J3T21/gAItar/solidworks/fret12_guide.SLDPRT

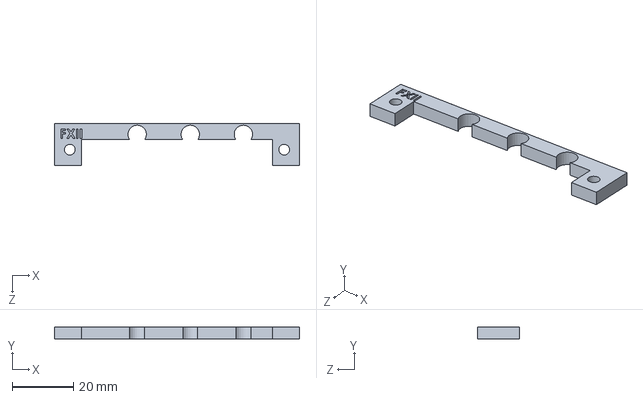
[picture p25: CAD file, 2025-05-29]
solidworks/fret12_guide.SLDPRT
80.0 x 4.00 x 13.8 mm
