J3T21/gAItar/solidworks/inside_helmet.SLDPRT

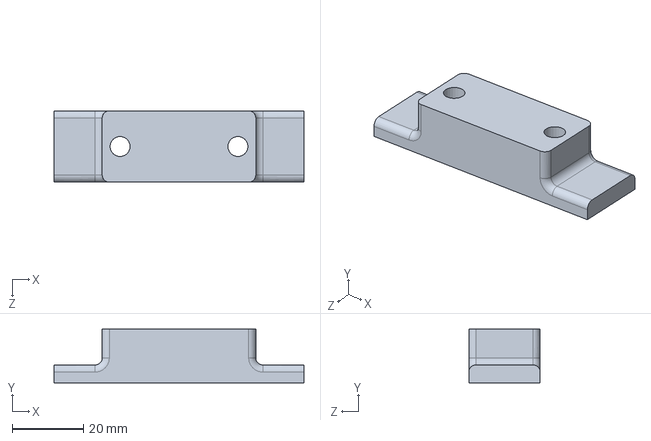
[picture p26: CAD file, 2025-05-04]
solidworks/inside_helmet.SLDPRT
70.0 x 15.0 x 20.0 mm
