J3T21/gAItar/solidworks/helmot_outer.SLDPRT

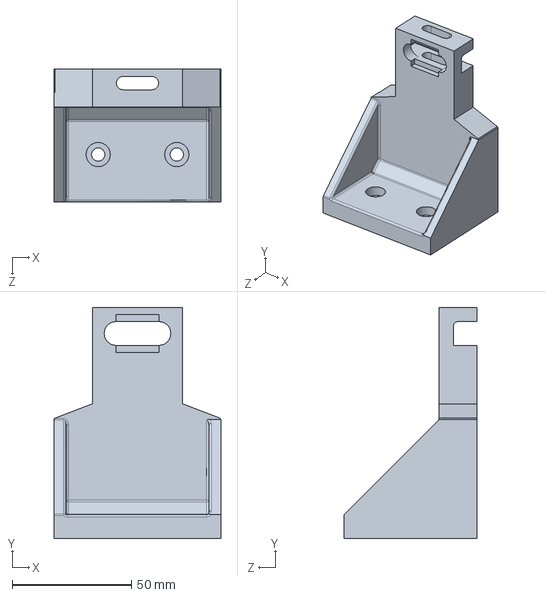
[picture p27: CAD file, 2025-05-04]
solidworks/helmot_outer.SLDPRT
70.0 x 97.0 x 56.0 mm
