J3T21/gAItar/solidworks/rh_26_3.SLDPRT

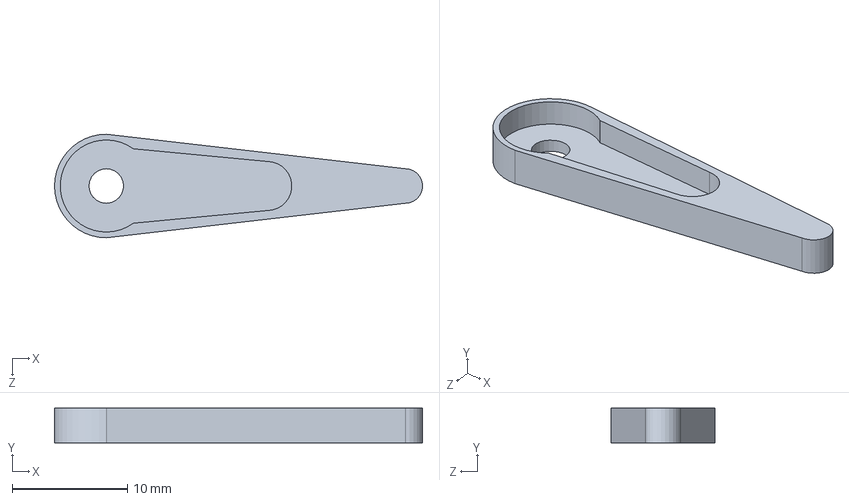
[picture p28: CAD file, 2025-04-07]
solidworks/rh_26_3.SLDPRT
32.0 x 3.00 x 9.00 mm
