J3T21/gAItar/solidworks/PCB_plate_n.STL

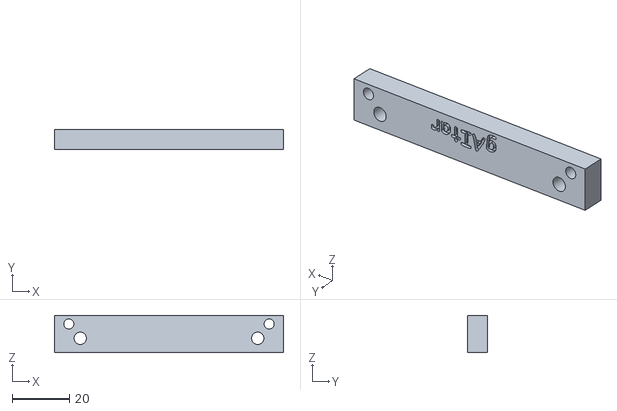
[picture p29: CAD file, 2025-04-07]
solidworks/PCB_plate_n.STL
80.0 x 7.00 x 13.0
