J3T21/gAItar/solidworks/rh_slotted.SLDPRT

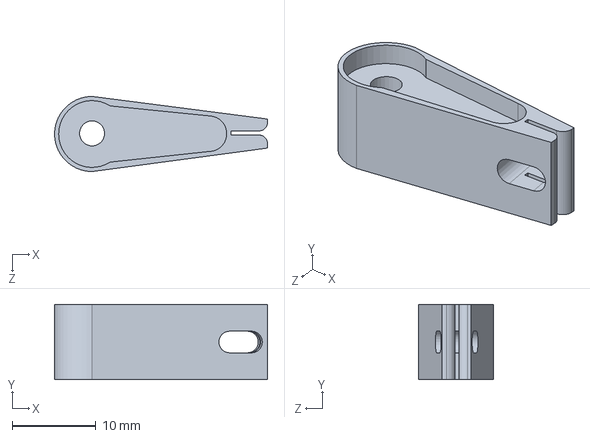
[picture p30: CAD file, 2025-04-07]
solidworks/rh_slotted.SLDPRT
25.5 x 9.00 x 9.00 mm
