J3T21/gAItar/solidworks/spacer.STL

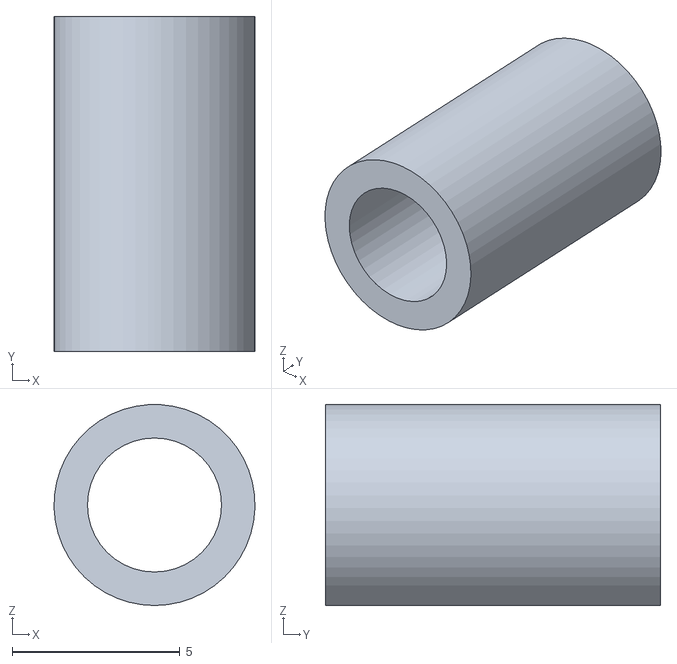
[picture p32: CAD file, 2025-04-07]
solidworks/spacer.STL
6.00 x 10.0 x 6.00
