J3T21/gAItar/solidworks/rh_27_3.STL

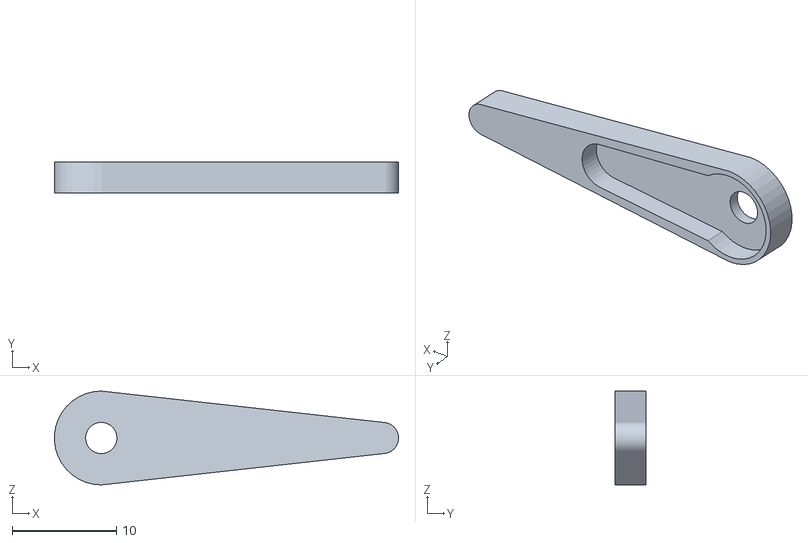
[picture p33: CAD file, 2025-04-07]
solidworks/rh_27_3.STL
33.0 x 3.00 x 9.00
