J3T21/gAItar/solidworks/rh_30_3_flex5.STL

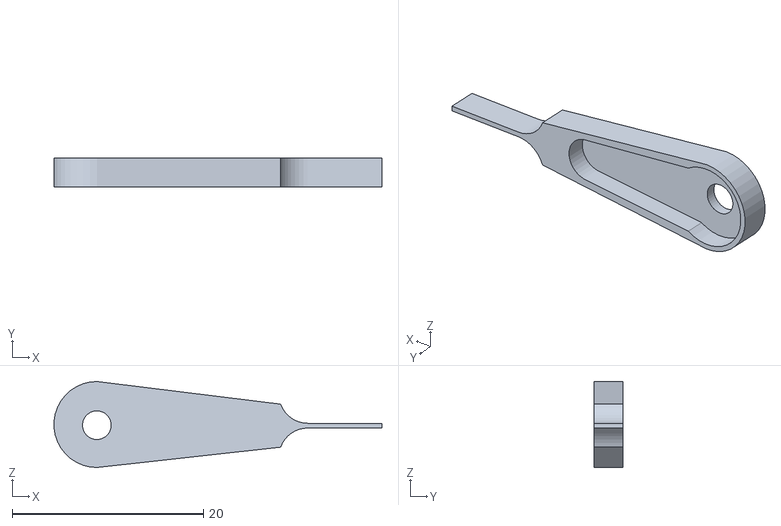
[picture p34: CAD file, 2025-04-07]
solidworks/rh_30_3_flex5.STL
34.3 x 3.00 x 9.00
