J3T21/gAItar/solidworks/Fret3_clamp.SLDPRT

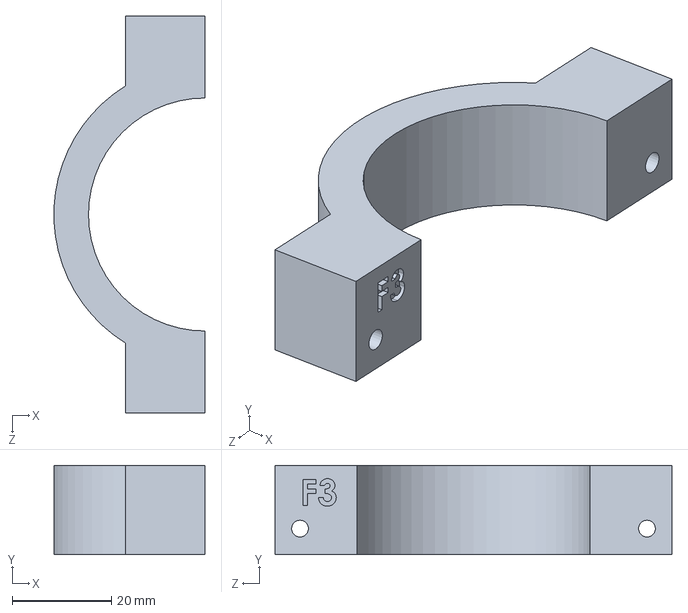
[picture p36: CAD file, 2025-04-04]
solidworks/Fret3_clamp.SLDPRT
30.5 x 18.0 x 80.0 mm
