J3T21/gAItar/solidworks/fret11_top.SLDPRT

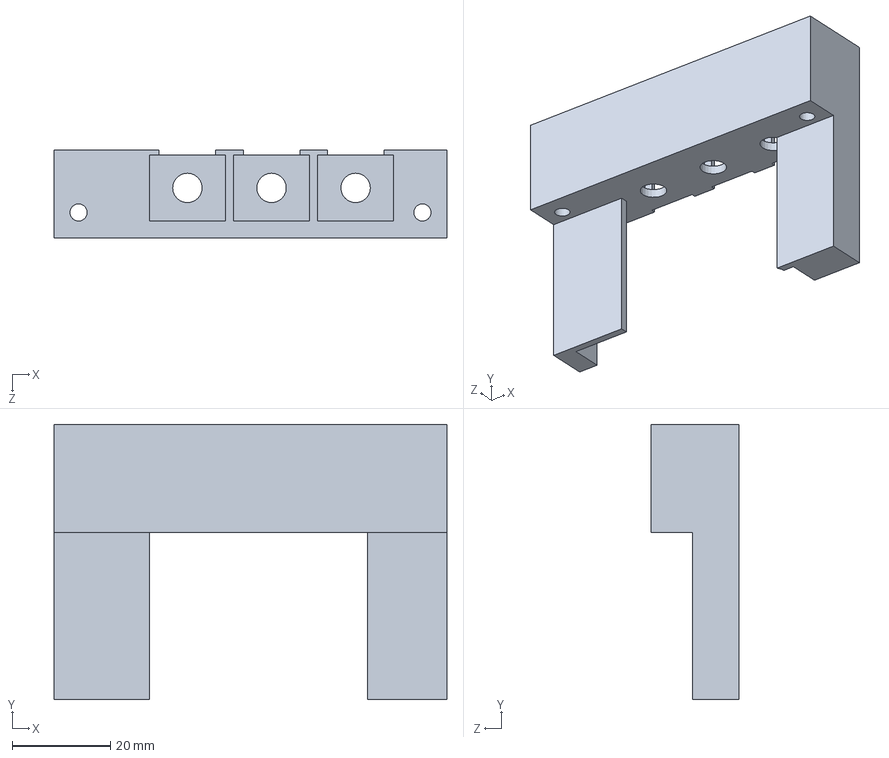
[picture p37: CAD file, 2025-04-04]
solidworks/fret11_top.SLDPRT
80.0 x 56.0 x 18.0 mm
