J3T21/gAItar/solidworks/fret2_guide.SLDPRT

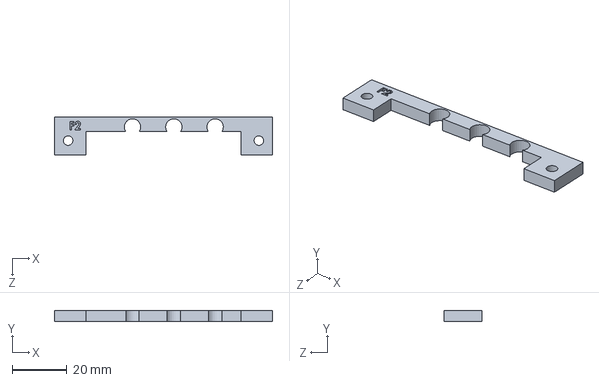
[picture p38: CAD file, 2025-04-04]
solidworks/fret2_guide.SLDPRT
80.0 x 4.00 x 13.8 mm
