J3T21/gAItar/solidworks/lh_fingerhigh_2.5.SLDPRT

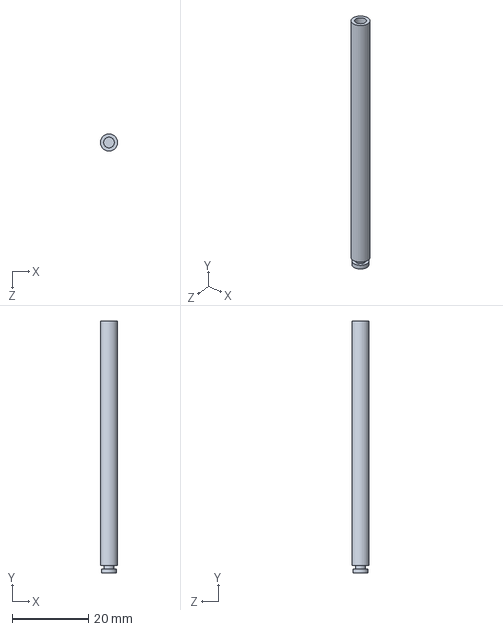
[picture p39: CAD file, 2025-04-04]
solidworks/lh_fingerhigh_2.5.SLDPRT
4.50 x 66.0 x 4.50 mm
