J3T21/gAItar/solidworks/fret8_top.SLDPRT

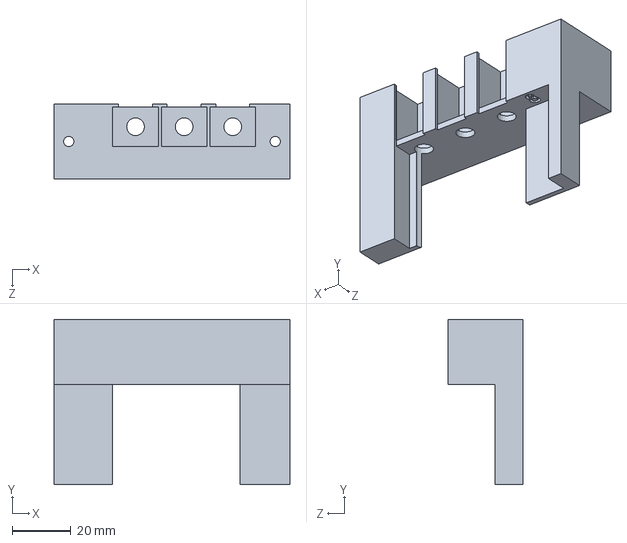
[picture p40: CAD file, 2025-04-04]
solidworks/fret8_top.SLDPRT
80.0 x 56.0 x 25.5 mm
