J3T21/gAItar/solidworks/Fret4_new.SLDPRT

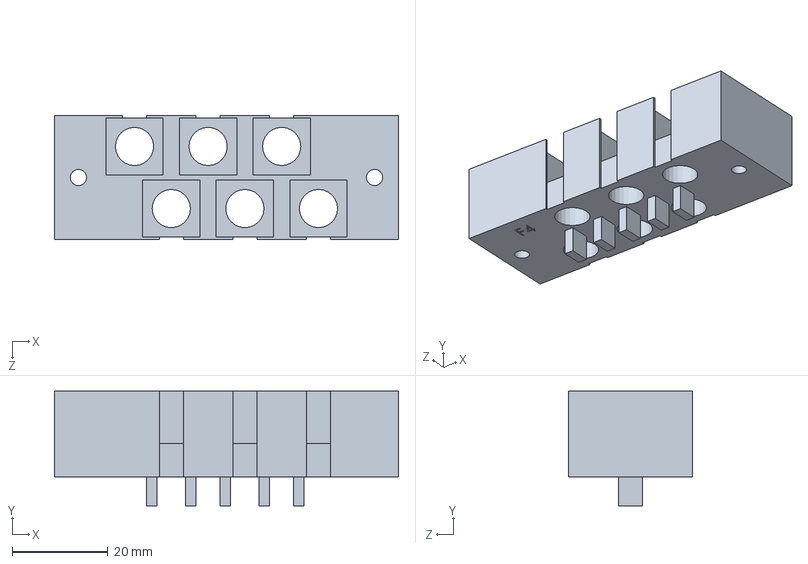
[picture p41: CAD file, 2025-04-04]
solidworks/Fret4_new.SLDPRT
72.0 x 24.0 x 26.0 mm
