J3T21/gAItar/solidworks/fret10_bottom.SLDPRT

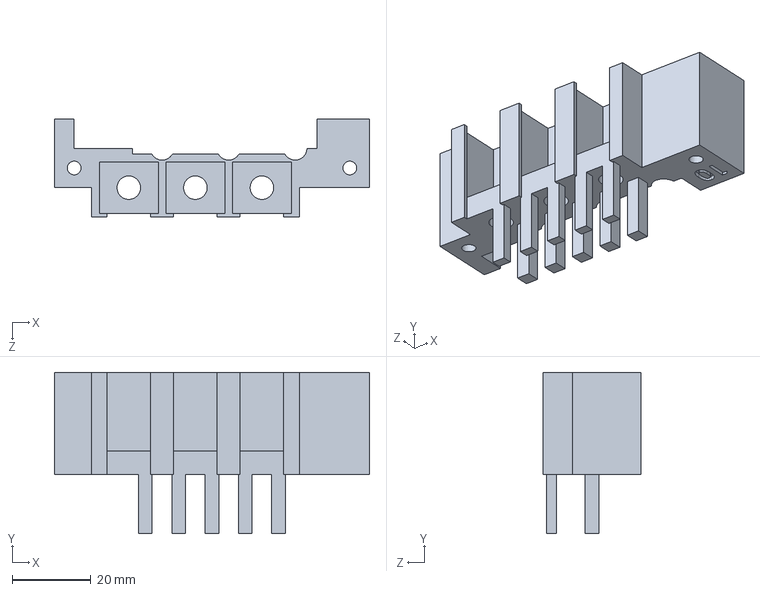
[picture p42: CAD file, 2025-04-04]
solidworks/fret10_bottom.SLDPRT
80.0 x 41.0 x 25.0 mm
