J3T21/gAItar/solidworks/Fret2_clampv2.SLDPRT

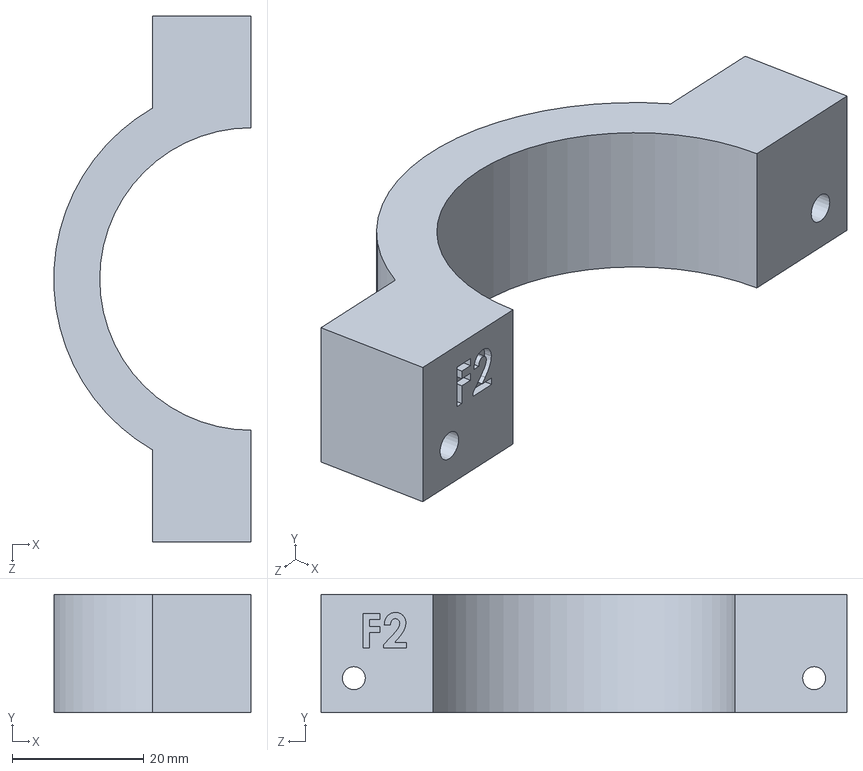
[picture p43: CAD file, 2025-04-04]
solidworks/Fret2_clampv2.SLDPRT
30.0 x 18.0 x 80.0 mm
