J3T21/gAItar/solidworks/Fret1_lid.SLDPRT

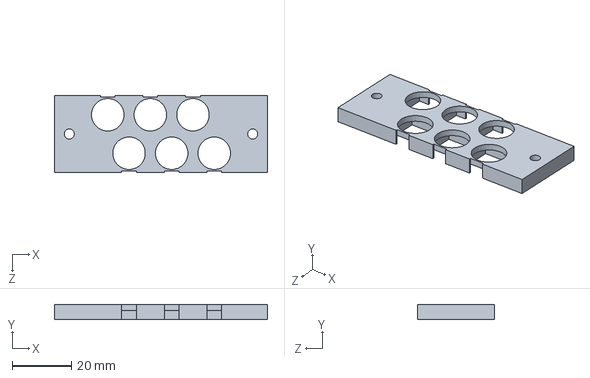
[picture p45: CAD file, 2025-04-04]
solidworks/Fret1_lid.SLDPRT
72.0 x 5.00 x 26.0 mm
