J3T21/gAItar/solidworks/lh_fingerhigh_3_5.SLDPRT

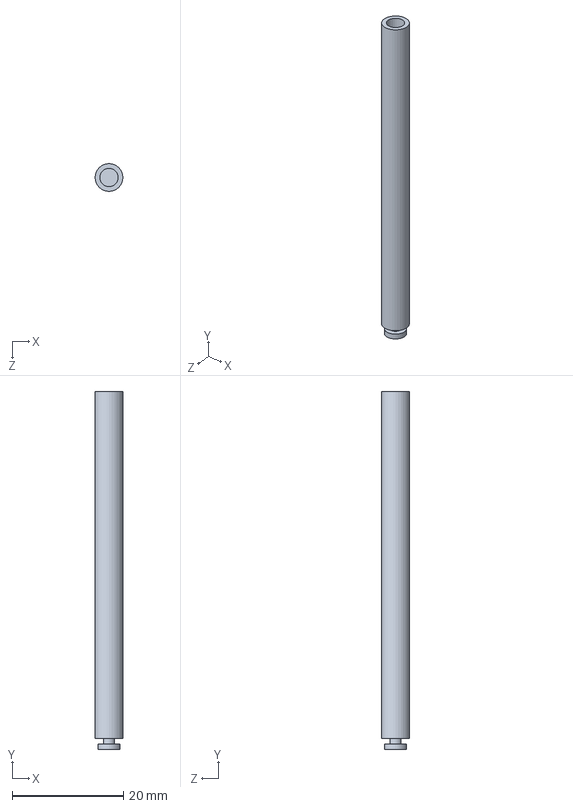
[picture p46: CAD file, 2025-04-04]
solidworks/lh_fingerhigh_3_5.SLDPRT
5.00 x 64.5 x 5.00 mm
