J3T21/gAItar/solidworks/shim.SLDPRT

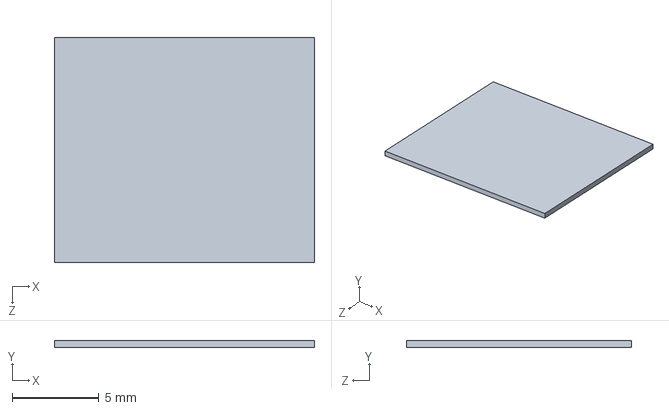
[picture p47: CAD file, 2025-04-04]
solidworks/shim.SLDPRT
15.0 x 0.4 x 13.0 mm
