J3T21/gAItar/solidworks/fret13_rework.SLDPRT

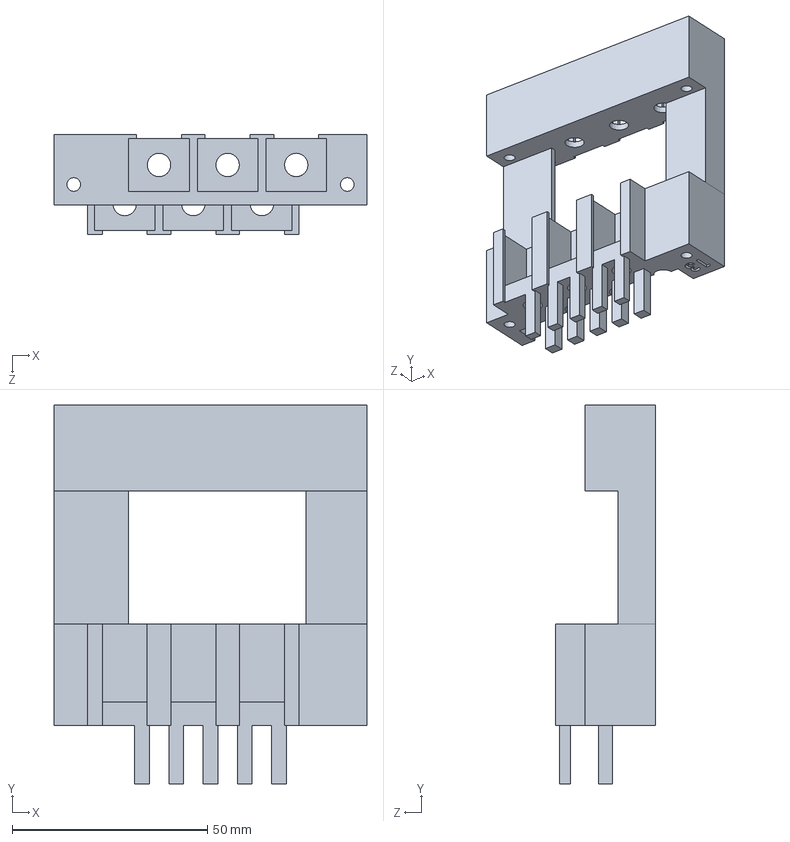
[picture p48: CAD file, 2025-04-04]
solidworks/fret13_rework.SLDPRT
80.0 x 97.0 x 25.5 mm
