J3T21/gAItar/solidworks/lh_finger_final_8_5m.STL

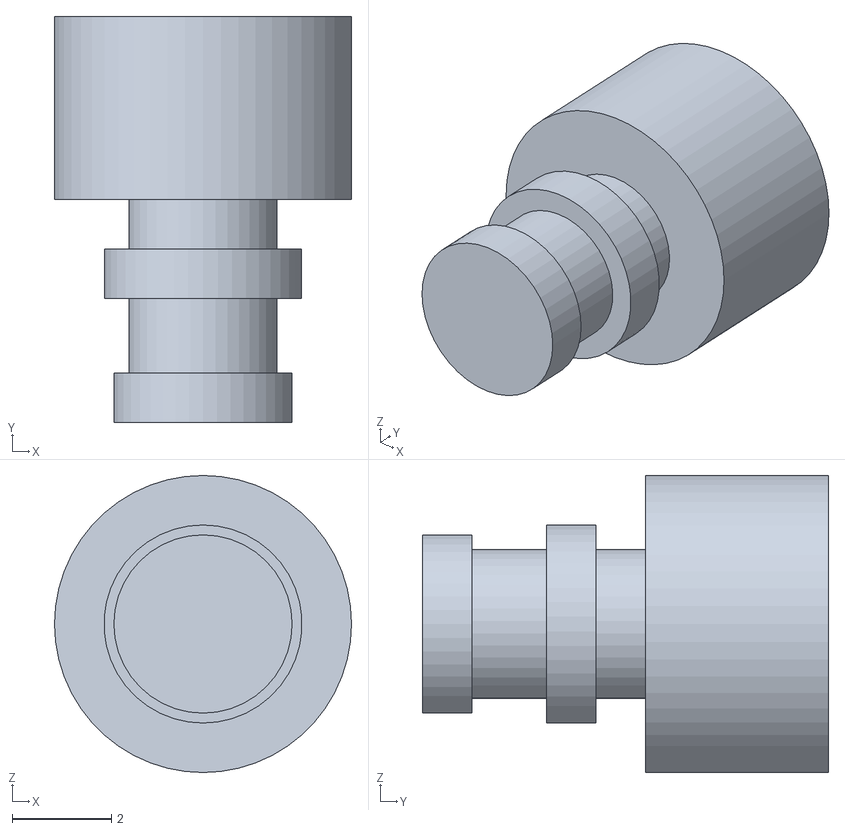
[picture p49: CAD file, 2025-04-04]
solidworks/lh_finger_final_8_5m.STL
6.00 x 8.20 x 6.00
