J3T21/gAItar/solidworks/fret3_bottom.SLDPRT

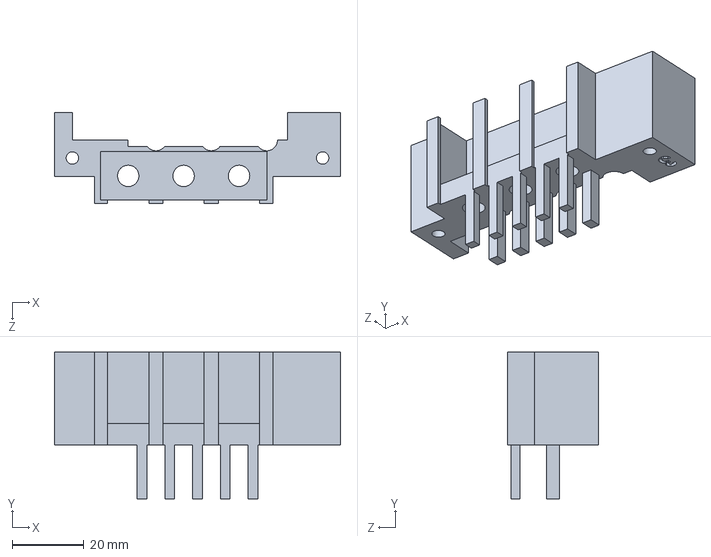
[picture p50: CAD file, 2025-04-04]
solidworks/fret3_bottom.SLDPRT
80.0 x 41.0 x 25.5 mm
