J3T21/gAItar/solidworks/fret10_top.SLDPRT

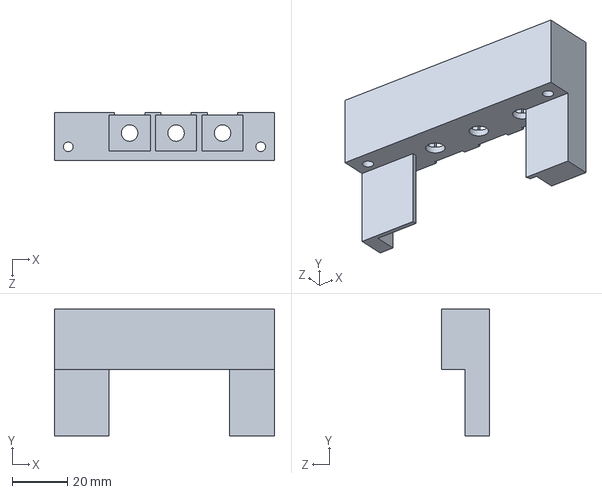
[picture p51: CAD file, 2025-04-04]
solidworks/fret10_top.SLDPRT
80.0 x 46.0 x 17.5 mm
