J3T21/gAItar/solidworks/Fret2_lid_long.STL

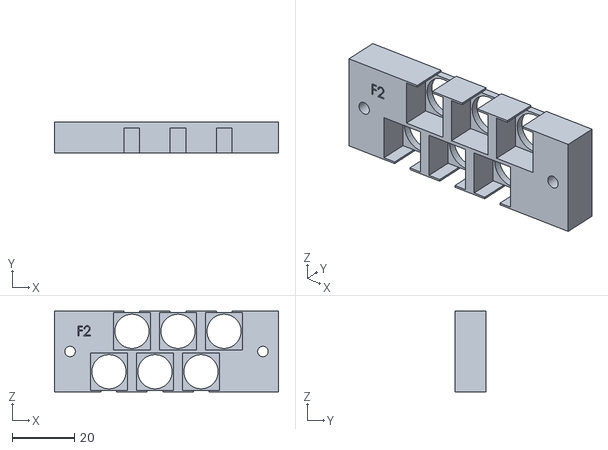
[picture p52: CAD file, 2025-04-04]
solidworks/Fret2_lid_long.STL
72.0 x 10.0 x 26.0
