J3T21/gAItar/solidworks/Fret6_lid_e.SLDPRT

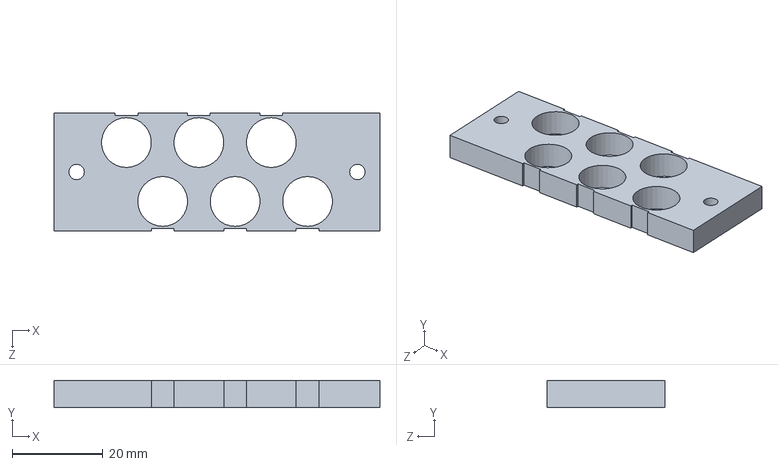
[picture p53: CAD file, 2025-04-04]
solidworks/Fret6_lid_e.SLDPRT
72.0 x 6.00 x 26.0 mm
