J3T21/gAItar/solidworks/lh_finger_8_5SH.SLDPRT

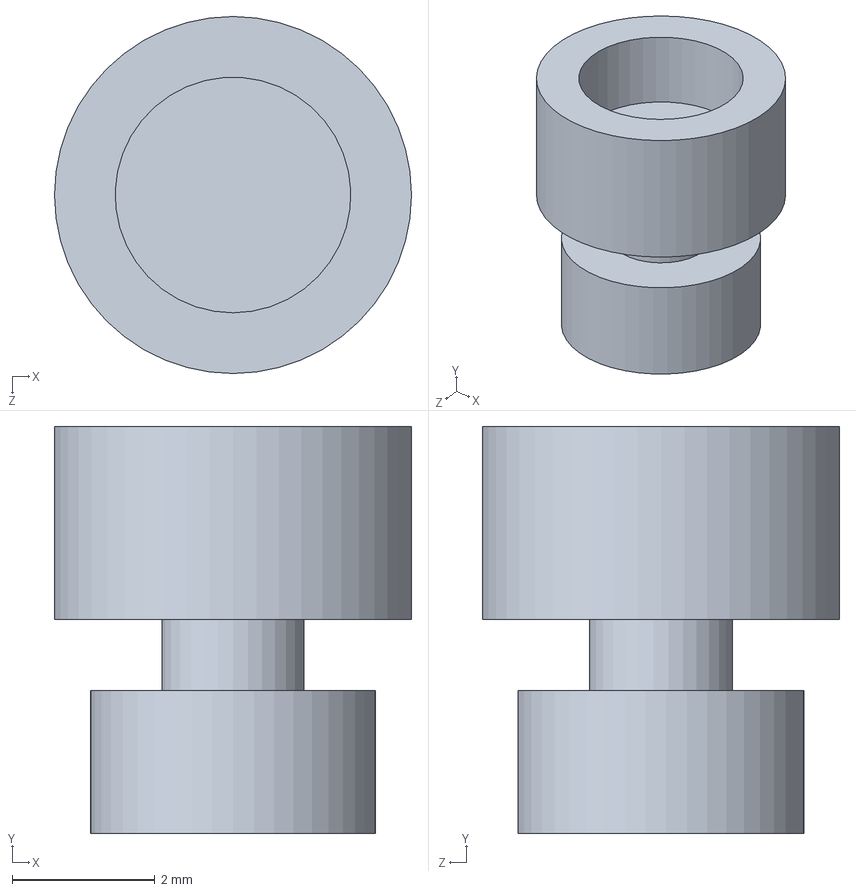
[picture p54: CAD file, 2025-04-04]
solidworks/lh_finger_8_5SH.SLDPRT
5.00 x 5.70 x 5.00 mm
