J3T21/gAItar/solidworks/m3socket.SLDPRT

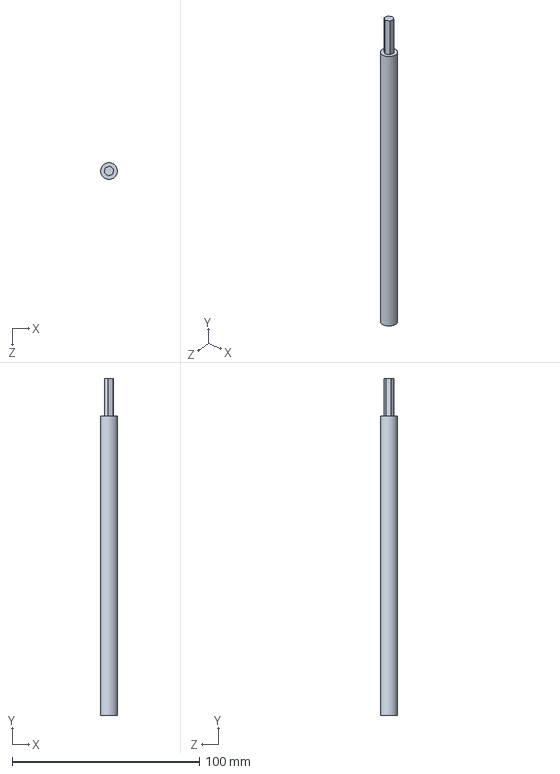
[picture p55: CAD file, 2025-04-04]
solidworks/m3socket.SLDPRT
8.99 x 180.0 x 9.00 mm
