J3T21/gAItar/solidworks/lh_fingerhigh_3.SLDPRT

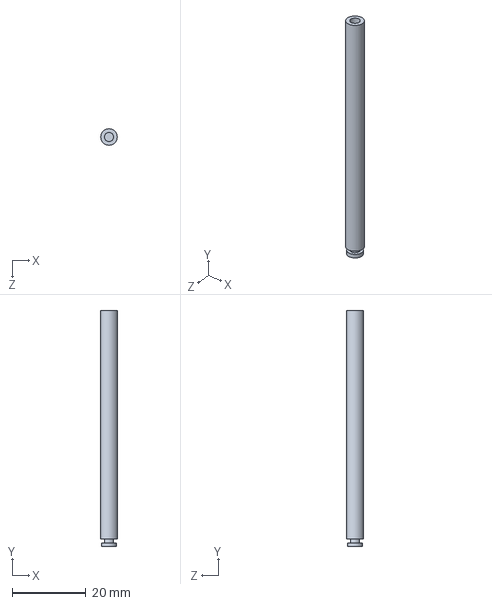
[picture p56: CAD file, 2025-04-04]
solidworks/lh_fingerhigh_3.SLDPRT
4.50 x 64.0 x 4.50 mm
