J3T21/gAItar/solidworks/lh_finger_8_SH.SLDPRT

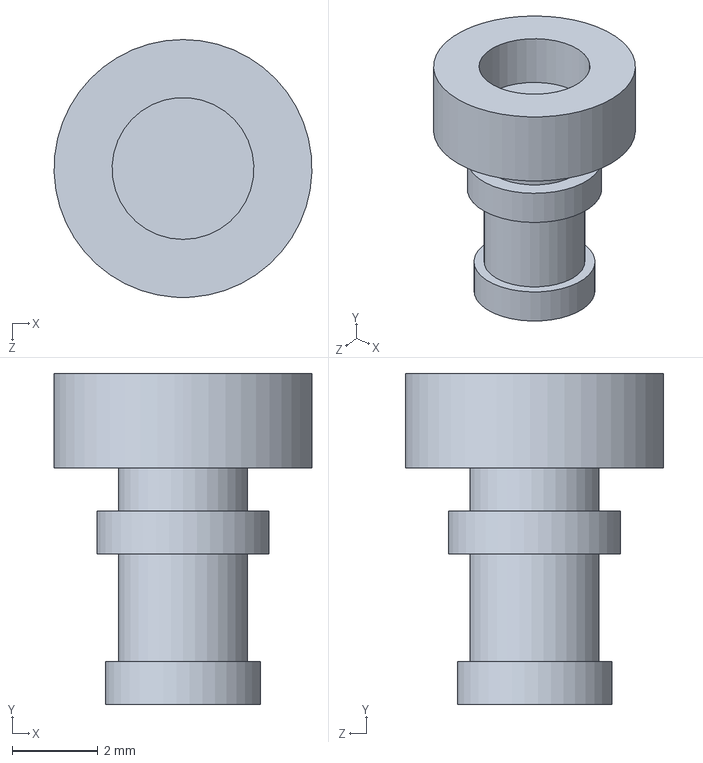
[picture p57: CAD file, 2025-04-04]
solidworks/lh_finger_8_SH.SLDPRT
6.00 x 7.70 x 6.00 mm
