J3T21/gAItar/solidworks/Fret6_clampv2.SLDPRT

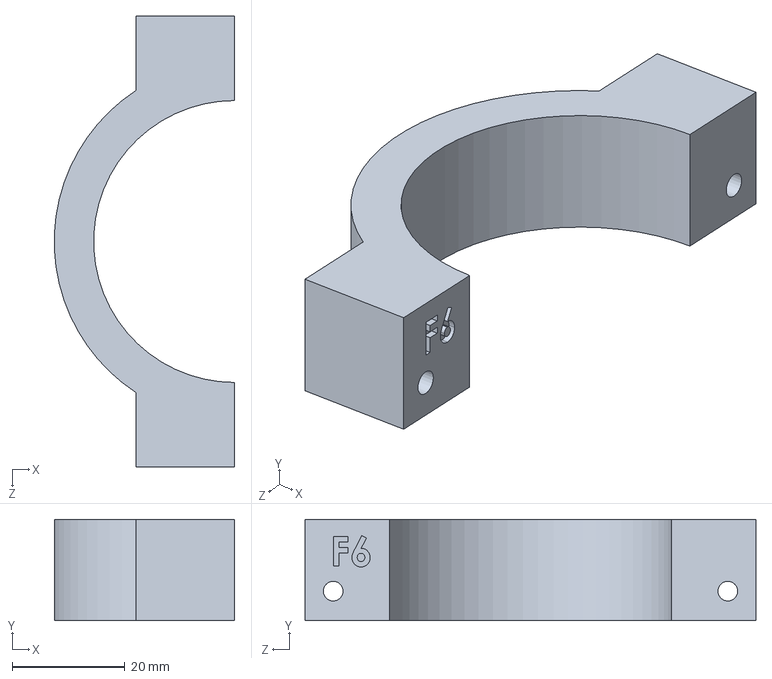
[picture p58: CAD file, 2025-04-04]
solidworks/Fret6_clampv2.SLDPRT
32.0 x 18.0 x 80.0 mm
