J3T21/gAItar/solidworks/Fret12_new.SLDPRT

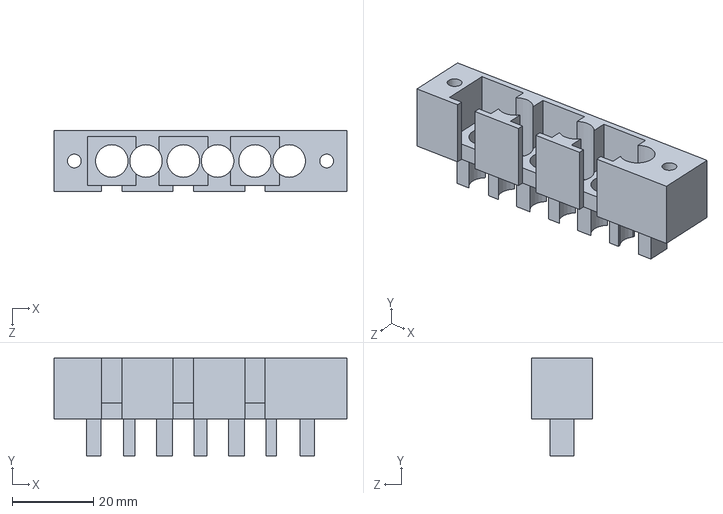
[picture p59: CAD file, 2025-04-04]
solidworks/Fret12_new.SLDPRT
72.0 x 24.0 x 15.0 mm
