J3T21/gAItar/solidworks/Fret5_lid.SLDPRT

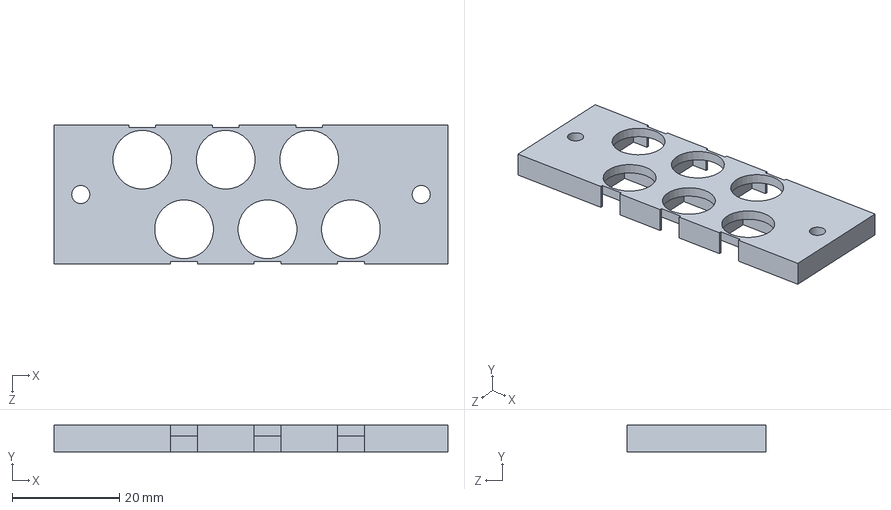
[picture p60: CAD file, 2025-04-04]
solidworks/Fret5_lid.SLDPRT
73.6 x 5.00 x 26.0 mm
