J3T21/gAItar/solidworks/fret13_bottom.SLDPRT

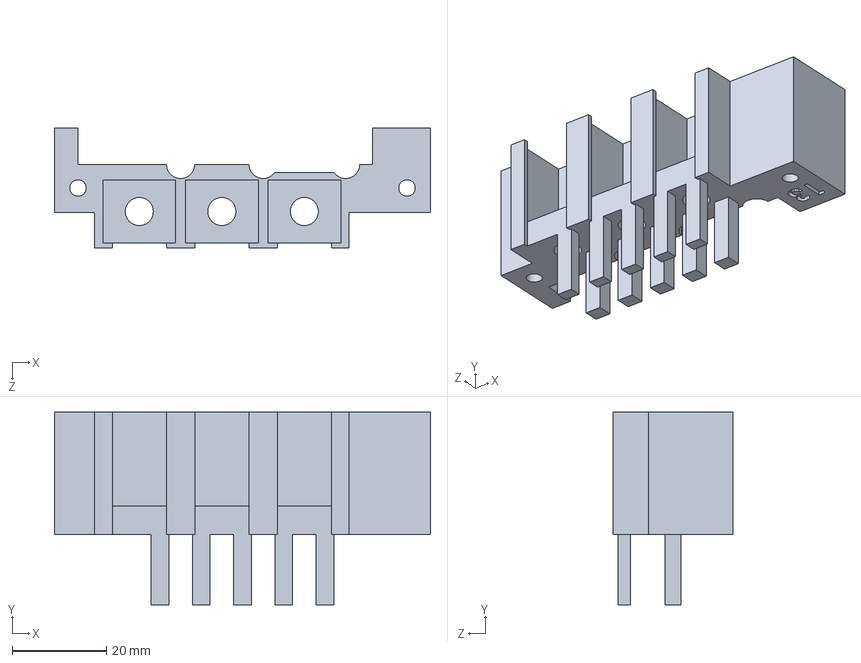
[picture p61: CAD file, 2025-04-04]
solidworks/fret13_bottom.SLDPRT
80.0 x 41.0 x 25.5 mm
