J3T21/gAItar/solidworks/lh_finger_final_7.SLDPRT

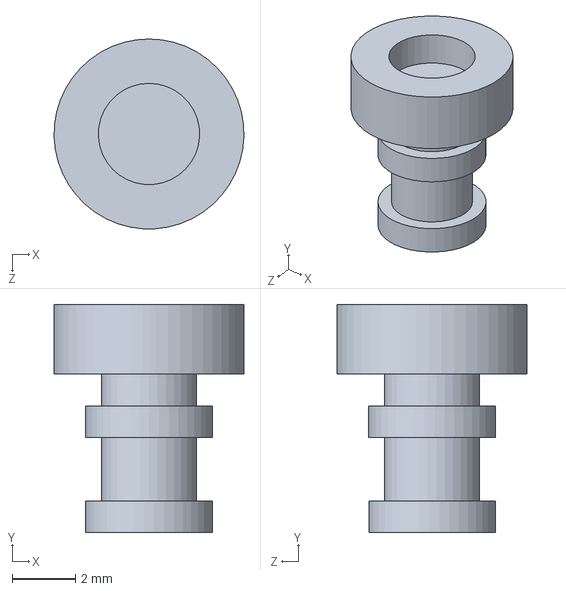
[picture p62: CAD file, 2025-04-04]
solidworks/lh_finger_final_7.SLDPRT
6.00 x 7.20 x 6.00 mm
