J3T21/gAItar/solidworks/lh_finger_3_5.SLDPRT

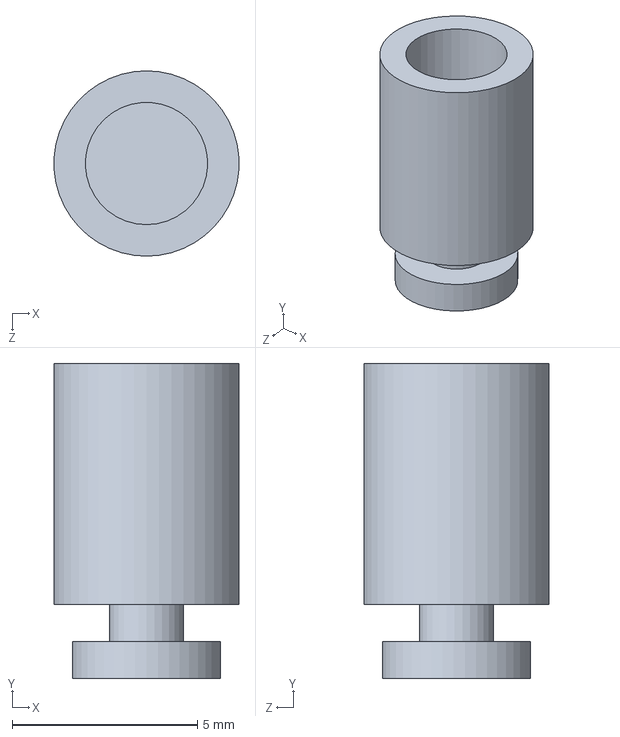
[picture p63: CAD file, 2025-04-04]
solidworks/lh_finger_3_5.SLDPRT
4.99 x 8.50 x 5.00 mm
