J3T21/gAItar/solidworks/fret7_bottom.SLDPRT

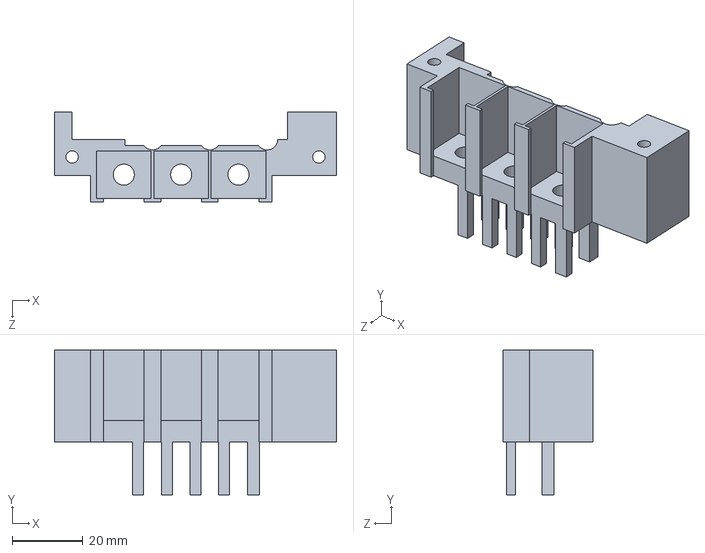
[picture p64: CAD file, 2025-04-04]
solidworks/fret7_bottom.SLDPRT
80.0 x 41.0 x 25.5 mm
