J3T21/gAItar/solidworks/Fret1_clampv2.SLDPRT

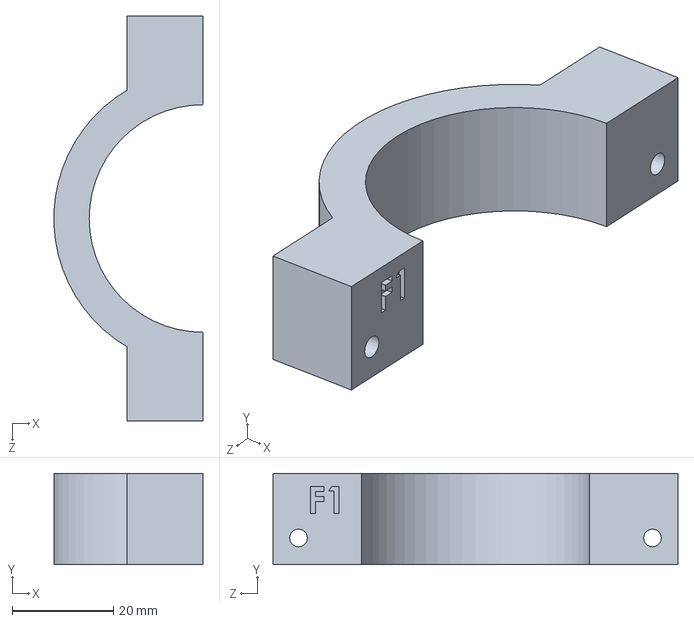
[picture p66: CAD file, 2025-04-04]
solidworks/Fret1_clampv2.SLDPRT
29.5 x 18.0 x 80.0 mm
