J3T21/gAItar/solidworks/Fret10_clampv2.SLDPRT

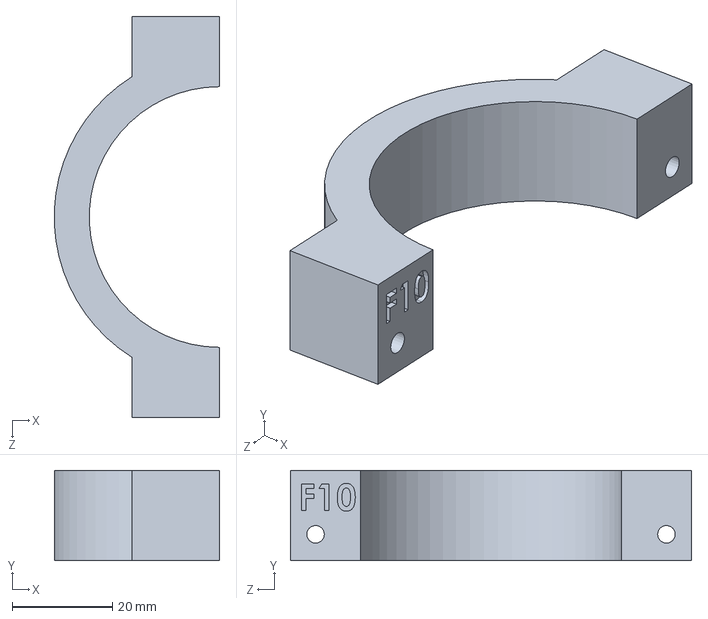
[picture p67: CAD file, 2025-04-04]
solidworks/Fret10_clampv2.SLDPRT
33.0 x 18.0 x 80.0 mm
