J3T21/gAItar/solidworks/lh_finger_final_8_5H.SLDPRT

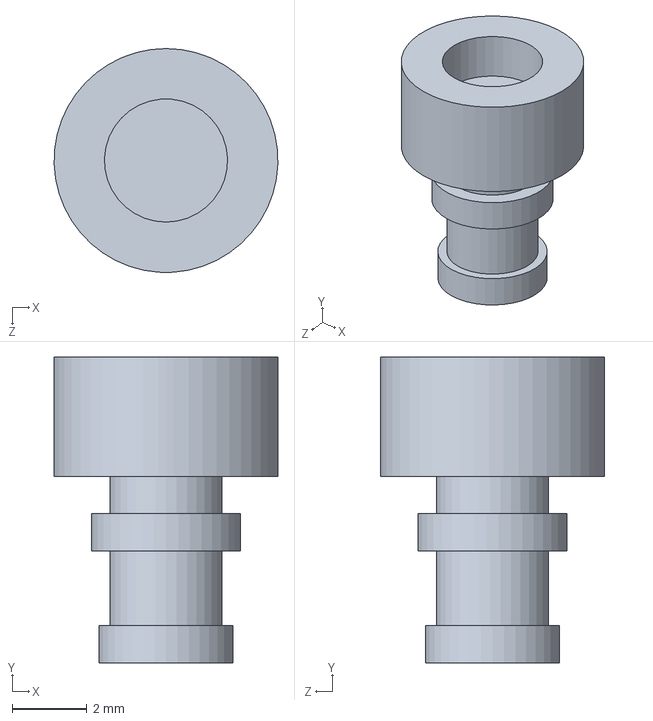
[picture p68: CAD file, 2025-04-04]
solidworks/lh_finger_final_8_5H.SLDPRT
6.00 x 8.20 x 6.00 mm
