J3T21/gAItar/solidworks/fret3_lidtop.SLDPRT

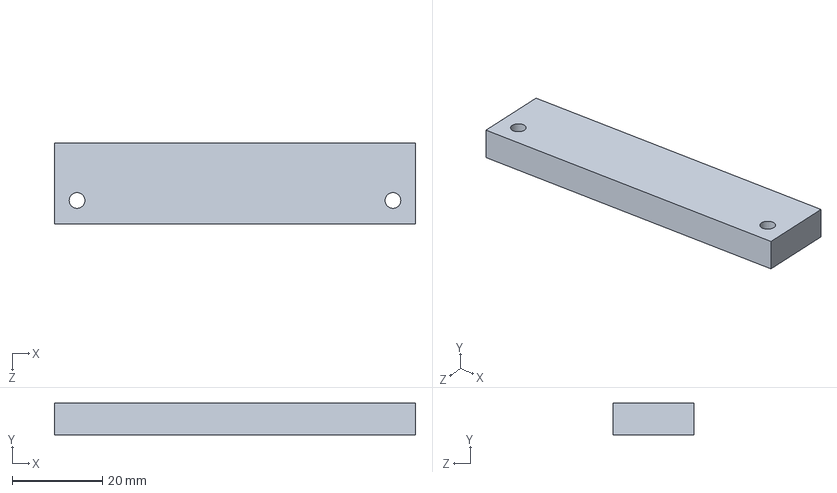
[picture p69: CAD file, 2025-04-04]
solidworks/fret3_lidtop.SLDPRT
80.0 x 7.00 x 18.0 mm
