J3T21/gAItar/solidworks/lh_finger_2.5.SLDPRT

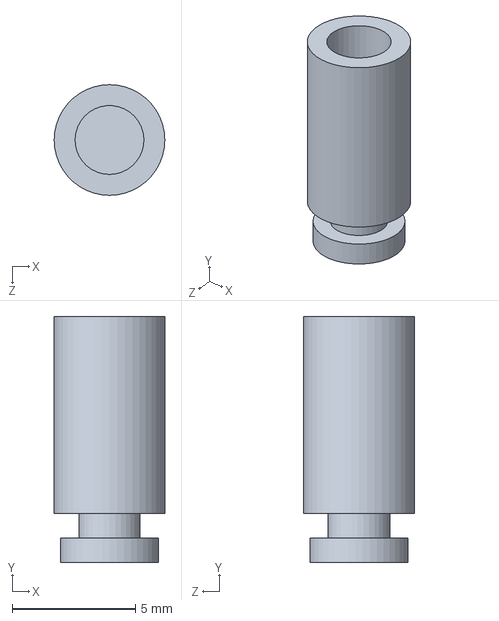
[picture p70: CAD file, 2025-04-04]
solidworks/lh_finger_2.5.SLDPRT
4.50 x 10.0 x 4.50 mm
