J3T21/gAItar/solidworks/lh_fingerhigh_deep.SLDPRT

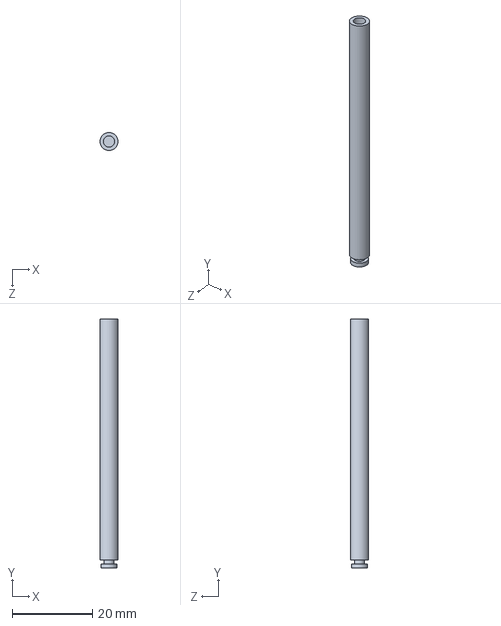
[picture p72: CAD file, 2025-04-04]
solidworks/lh_fingerhigh_deep.SLDPRT
4.50 x 62.0 x 4.50 mm
