J3T21/gAItar/solidworks/fret5_lidbottom.SLDPRT

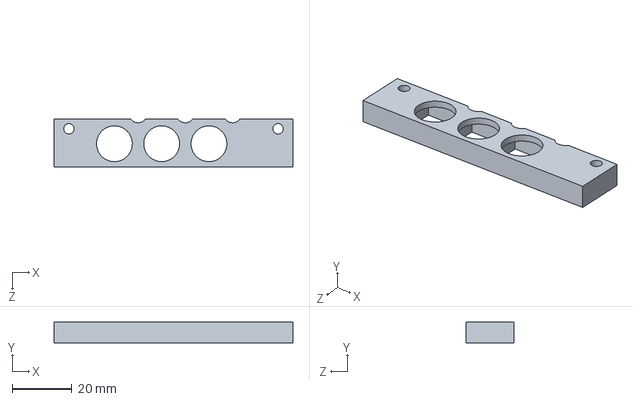
[picture p73: CAD file, 2025-04-04]
solidworks/fret5_lidbottom.SLDPRT
80.0 x 7.00 x 16.0 mm
