J3T21/gAItar/solidworks/yasser.SLDPRT

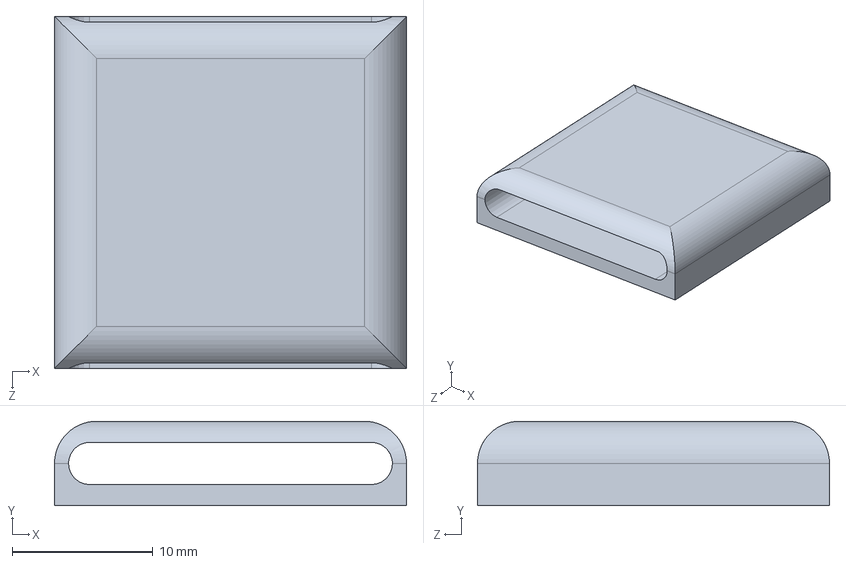
[picture p74: CAD file, 2025-04-04]
solidworks/yasser.SLDPRT
25.0 x 6.00 x 25.0 mm
