J3T21/gAItar/solidworks/Fret4_clampv2.SLDPRT

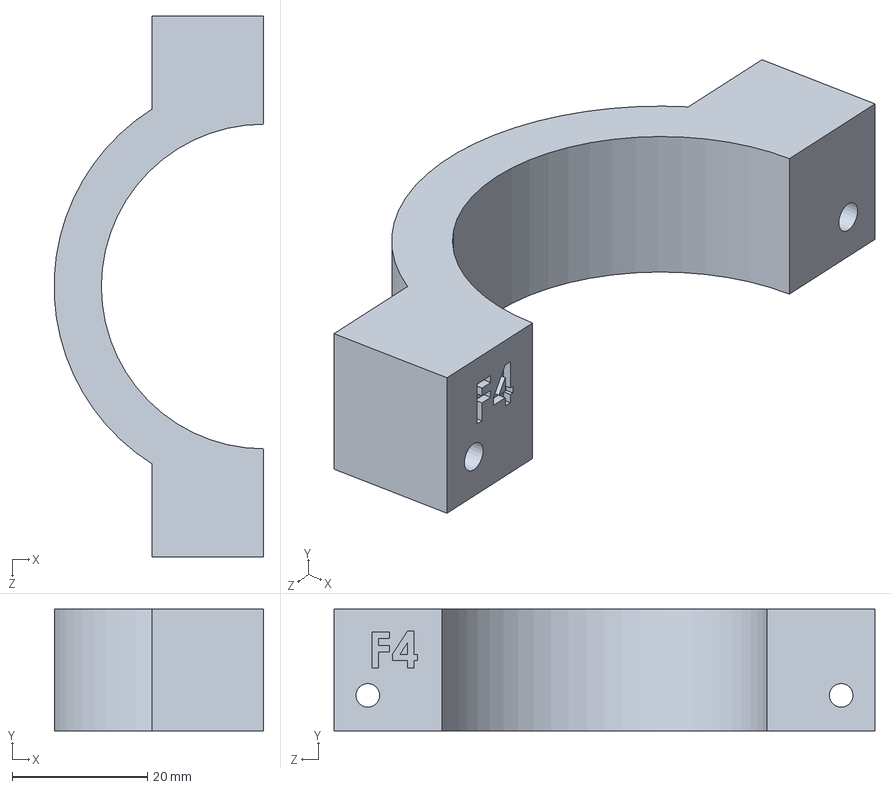
[picture p75: CAD file, 2025-04-04]
solidworks/Fret4_clampv2.SLDPRT
31.0 x 18.0 x 80.0 mm
