J3T21/gAItar/solidworks/Fret5_lid_e.SLDPRT

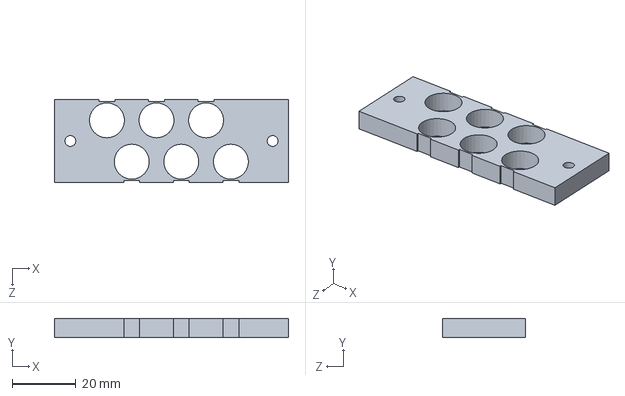
[picture p76: CAD file, 2025-04-04]
solidworks/Fret5_lid_e.SLDPRT
73.6 x 6.00 x 26.0 mm
