J3T21/gAItar/solidworks/lh_finger_3.SLDPRT

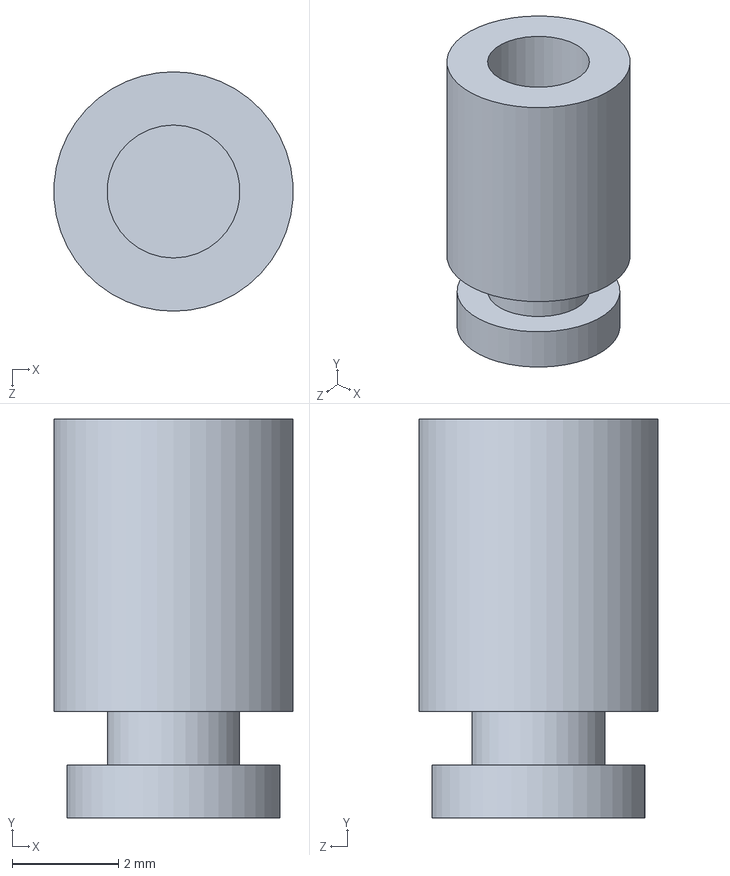
[picture p77: CAD file, 2025-04-04]
solidworks/lh_finger_3.SLDPRT
4.49 x 7.50 x 4.50 mm
