J3T21/gAItar/solidworks/fret3_rework.SLDPRT

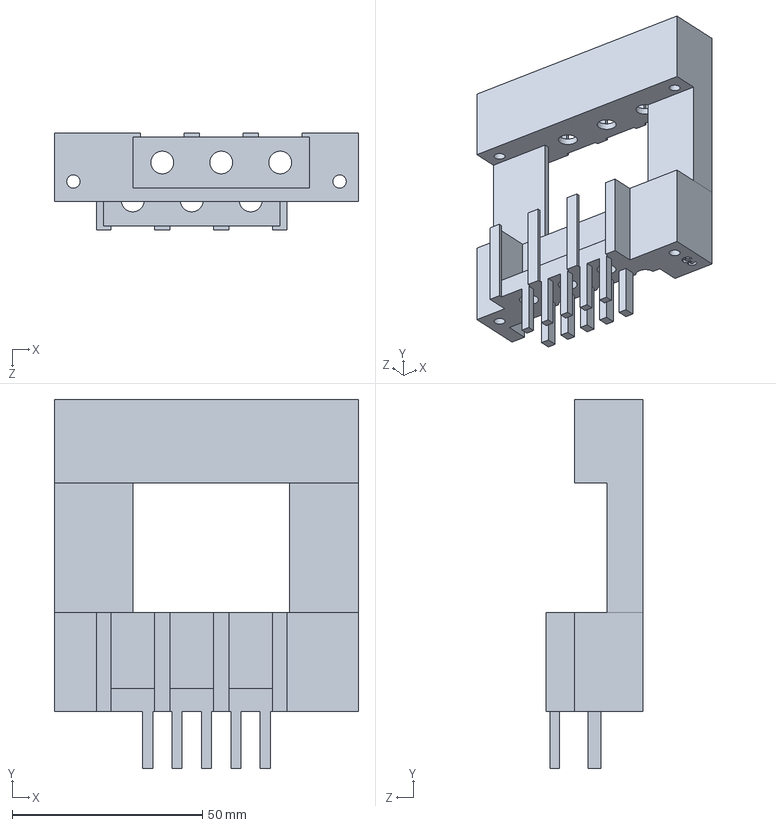
[picture p78: CAD file, 2025-04-04]
solidworks/fret3_rework.SLDPRT
80.0 x 97.0 x 25.5 mm
