J3T21/gAItar/solidworks/lh_finger_final_ext.SLDPRT

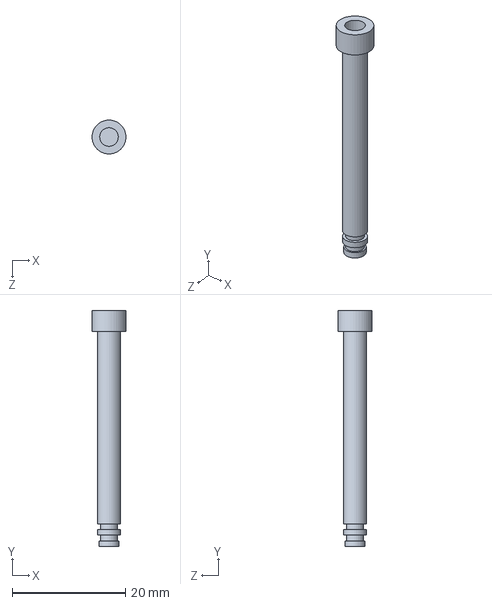
[picture p79: CAD file, 2025-04-04]
solidworks/lh_finger_final_ext.SLDPRT
5.99 x 41.7 x 6.00 mm
