J3T21/gAItar/solidworks/Fret5_clampv2.SLDPRT

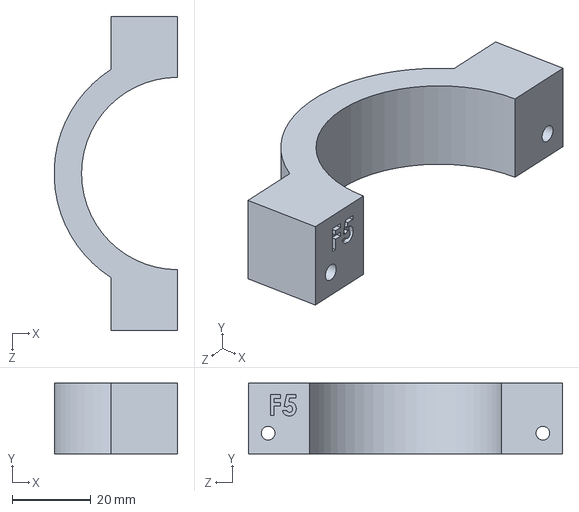
[picture p80: CAD file, 2025-04-04]
solidworks/Fret5_clampv2.SLDPRT
31.5 x 18.0 x 80.0 mm
