J3T21/gAItar/solidworks/lh_finger_2.SLDPRT

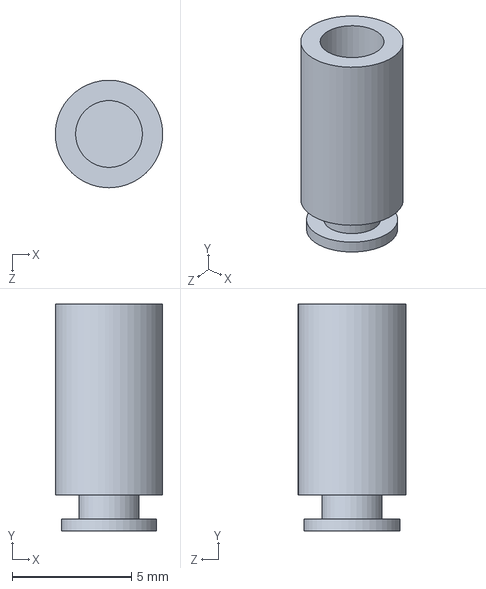
[picture p81: CAD file, 2025-04-04]
solidworks/lh_finger_2.SLDPRT
4.50 x 9.50 x 4.50 mm
