J3T21/gAItar/gAItar_arduino/src/pwm_shift_solenoid.h

#ifndef PWM_SHIFT_SOLENOID_H
#define PWM_SHIFT_SOLENOID_H

#include "globals.h"
#include "shift_solenoid.h"

// Declare the functions
void pwmRampPress(int fretIndex, int stringIndex, int targetBrightness, int holdMs, float rampTime);
void pwmLogRampPress(int fretIndex, int stringIndex, int targetBrightness, int holdMs, float rampTime);
void pwmSineRampPress(int fretIndex, int stringIndex, int targetBrightness, int holdMs, float rampTime);
void softStart(int clkPin, int dataPin, int clearPin, byte fretState, byte softStartMask, SoftStartState &state);

#endif // PWM_SHIFT_SOLENOID_H
